shaharsery/5V-Power-Bank/Battery Charger Rev 0.4/Battery Charger Rev 0.4.sch

## KiCad design Battery Charger Rev 0.4/Battery Charger Rev 0.4.sch (2020-07-28)

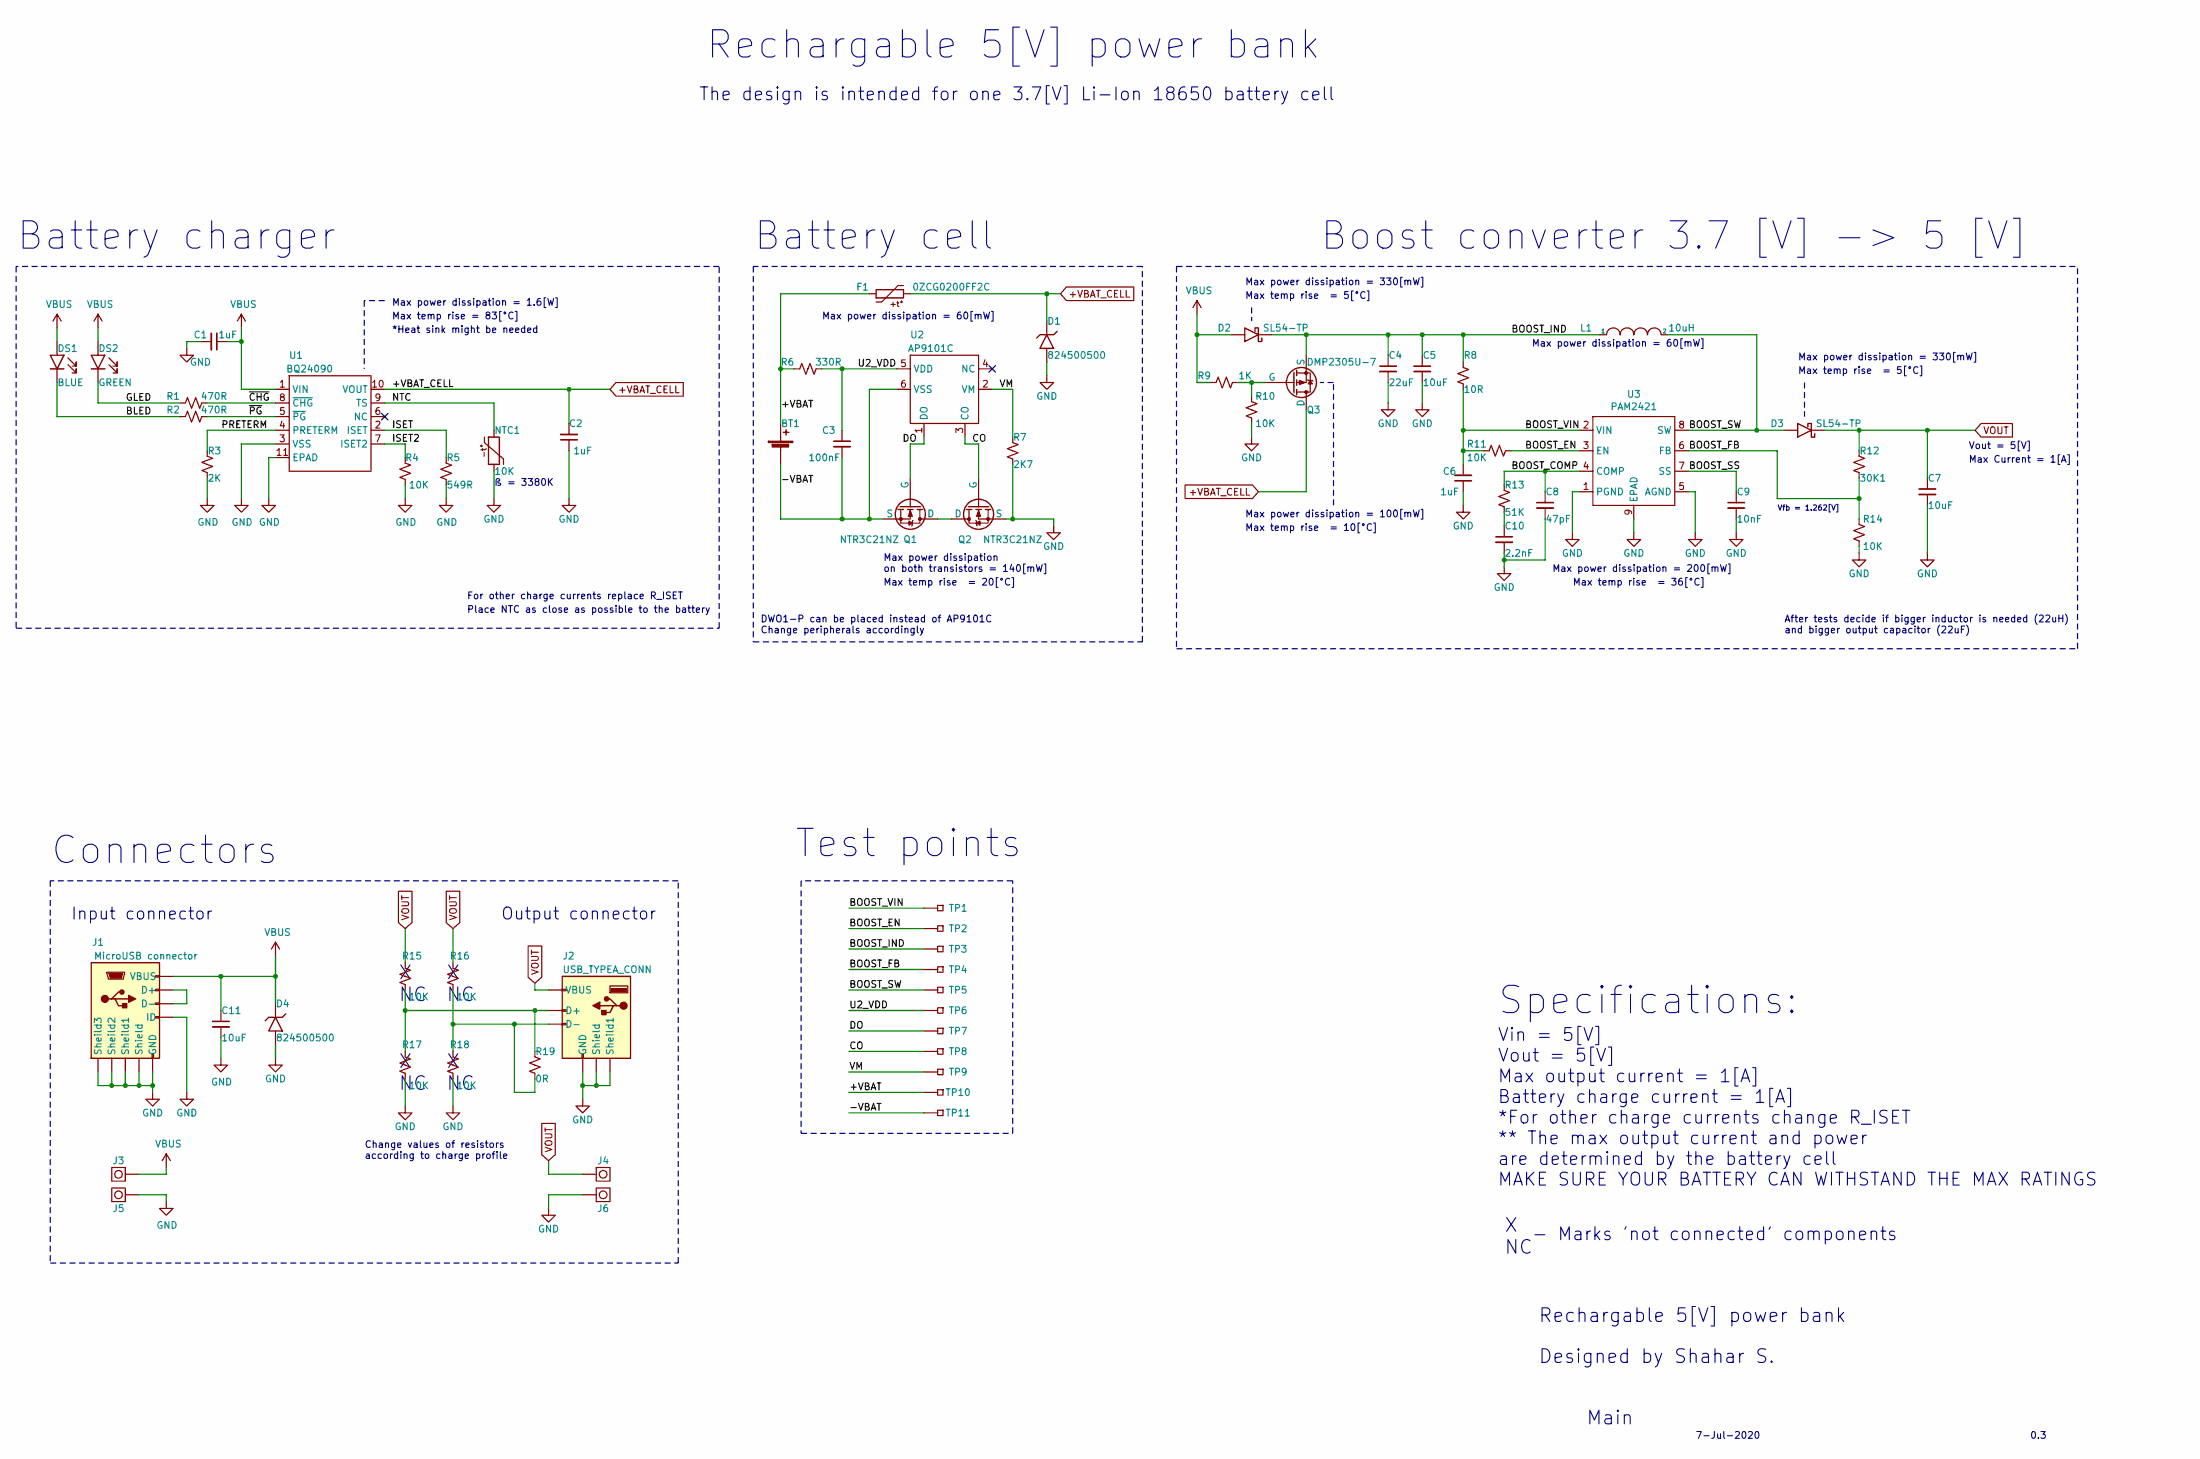
[picture p16: schematic Battery Charger Rev 0.4.sch]

Parts:
BT1: 18650 Li-ion Battery Cell
C1, C2, C6: CAPC_1uF_0603; C_0603_1608Metric_Pad1.05x0.95mm_HandSolder; Manufacturer_PN CL10B105MO8NNWC
C3: CAPC_100nF_0603; C_0603_1608Metric_Pad1.05x0.95mm_HandSolder; Manufacturer_PN CC0603KRX7R8BB104
C4: CAPC_22uF_1210; C_1210_3225Metric_Pad1.42x2.65mm_HandSolder; Manufacturer_PN C1210C226K4PACTU
C5: CAPC_10uF_0805; C_0805_2012Metric_Pad1.15x1.40mm_HandSolder; Manufacturer_PN C0805C106K4PACTU
C7: CAPC_10uF_1210; C_1210_3225Metric_Pad1.42x2.65mm_HandSolder; Manufacturer_PN C1210C106M4PACTU
C8: CAPC_47pF_0603; C_0603_1608Metric_Pad1.05x0.95mm_HandSolder; Manufacturer_PN C0603C470J1GACTU
C9: CAPC_10nF_0603; C_0603_1608Metric_Pad1.05x0.95mm_HandSolder; Manufacturer_PN CC0603KRX7R9BB103
C10: CAPC_2.2nF_0603; C_0603_1608Metric_Pad1.05x0.95mm_HandSolder; Manufacturer_PN C0603C222J5RACTU
C11: CAPC_10uF_0603; C_0603_1608Metric_Pad1.05x0.95mm_HandSolder; Manufacturer_PN GRM188R61E106KA73D
D1, D4: TVS_5V_9.2V_DO214AC; Manufacturer_PN 824500500
D2, D3: Schottky_40V_5A_DO-214AB; Manufacturer_PN SL54-TP
DS1: LEDC_BLUE_0603; LED_0603_1608Metric_Pad1.05x0.95mm_HandSolder; Manufacturer_PN 150060BS75000
DS2: LEDC_GREEN_0603; LED_0603_1608Metric_Pad1.05x0.95mm_HandSolder; Manufacturer_PN 150060VS75000
F1: PTC_POLYFUSE_8V_2A_1812; Manufacturer_PN 0ZCG0200FF2C
J1: Micro_USB_CONN; Manufacturer_PN MCR-B-S-RA-SMT-EH4B-T/R
J2: USB-A_CONN; Manufacturer_PN 292303-1
J3, J4, J5, J6: 1POS_CONN_PAD_30X30MM_H1MM; Manufacturer_PN N/A
L1: INDC_10uH_CDRH104R; Manufacturer_PN CDRH104RNP-100NC
NTC1: NTC_10K_3380K_0603; Manufacturer_PN NCU18XH103F60RB
Q1, Q2: NMOS_20V_3.6A_SOT-23-3; Manufacturer_PN NTR3C21NZT1G
Q3: PMOS_20V_4.2A_SOT-23-3; Manufacturer_PN DMP2305U-7
R1, R2: RESC_470R_0603; R_0603_1608Metric_Pad1.05x0.95mm_HandSolder; Manufacturer_PN RC0603JR-07470RL
R3: RESC_2K_0603; R_0603_1608Metric_Pad1.05x0.95mm_HandSolder; Manufacturer_PN RK73H1JTTD2001F
R4, R10, R11, R14, R15, R16, R17, R18: RESC_10K_0603; R_0603_1608Metric_Pad1.05x0.95mm_HandSolder; Manufacturer_PN RNCP0603FTD10K0
R5: RESC_549R_0603; R_0603_1608Metric_Pad1.05x0.95mm_HandSolder; Manufacturer_PN RK73H1JTTD5490F
R6: RESC_330R_0603; R_0603_1608Metric_Pad1.05x0.95mm_HandSolder; Manufacturer_PN ERJ-3EKF3300V
R7: RESC_2K7_0603; R_0603_1608Metric_Pad1.05x0.95mm_HandSolder; Manufacturer_PN CRGCQ0603F2K7
R8: RESC_10R_0603; R_0603_1608Metric_Pad1.05x0.95mm_HandSolder; Manufacturer_PN CRGH0603J10R
R9: RESC_1K_0603; R_0603_1608Metric_Pad1.05x0.95mm_HandSolder; Manufacturer_PN RC0603JR-071KL
R12: RESC_30K1_0603; R_0603_1608Metric_Pad1.05x0.95mm_HandSolder; Manufacturer_PN RMCF0603FT30K1
R13: RESC_51K_0603; R_0603_1608Metric_Pad1.05x0.95mm_HandSolder; Manufacturer_PN RMCF0603FT51K0
R19: RESC_0R_0603; R_0603_1608Metric_Pad1.05x0.95mm_HandSolder; Manufacturer_PN RC0603JR-070RL
TP1, TP2, TP3, TP4, TP5, TP6, TP7, TP8, TP9, TP10, TP11: TP_12.5X12.5_MM; Manufacturer_PN N/A
U1: BQ24090DGQR; Manufacturer_PN BQ24090DGQR
U2: AP9101C; SOT-23-6_Handsoldering; Manufacturer_PN AP9101CK6-ADTRG1
U3: PAM2421; Manufacturer_PN PAM2421AECADJR

Connections:
+VBAT: BT1.1 (+), F1.1, R6.2, TP10.1
+VBAT_CELL: C2.2, D1.K, F1.2, Q3.D, U1.10 (VOUT)
-VBAT: BT1.2 (-), C3.2, Q1.S, TP11.1, U2.6 (VSS)
BLED: DS1.K, R2.2
BOOST_COMP: C8.1, R13.1, U3.4 (COMP)
BOOST_EN: R11.2, TP2.1, U3.3 (EN)
BOOST_FB: R12.2, R14.2, TP4.1, U3.6 (FB)
BOOST_IND: C4.1, C5.1, D2.K, L1.1, Q3.S, R8.1, TP3.1
BOOST_SS: C9.1, U3.7 (SS)
BOOST_SW: D3.A, L1.2, TP5.1, U3.8 (SW)
BOOST_VIN: C6.2, R8.2, R11.1, TP1.1, U3.2 (VIN)
CO: Q2.G, TP8.1, U2.3 (CO)
DO: Q1.G, TP7.1, U2.1 (DO)
GLED: DS2.K, R1.2
GND: C1.2, C2.1, C4.2, C5.2, C6.1, C7.2, C8.2, C9.2, C10.2, C11.2, D1.A, D4.A, J1.4 (ID), J1.5 (GND), J1.6 (Shield), J1.7 (Sheild1), J1.8 (Sheild2), J1.9 (Sheild3), J2.4 (GND), J2.5 (Shield), J2.~ (Sheild1), J5.1, J6.1, NTC1.2, Q2.S, R3.2, R4.1, R5.2, R7.2, R10.1, R14.1, R17.1, R18.1, U1.3 (VSS), U1.11 (EPAD), U3.1 (PGND), U3.5 (AGND), U3.9 (EPAD)
ISET: R5.1, U1.2 (ISET)
ISET2: R4.2, U1.7 (ISET2)
NTC: NTC1.1, U1.9 (TS)
unnamed: C10.1, R13.2
unnamed: J1.2 (D-), J1.3 (D+)
unnamed: J2.2 (D-), R16.1, R18.2, R19.2
unnamed: J2.3 (D+), R15.1, R17.2, R19.1
unnamed: Q1.D, Q2.D
unnamed: Q3.G, R9.1, R10.2
PRETERM: R3.1, U1.4 (PRETERM)
U2_VDD: C3.1, R6.1, TP6.1, U2.5 (VDD)
VBUS: C1.1, C11.1, D2.A, D4.K, DS1.A, DS2.A, J1.1 (VBUS), J3.1, R9.2, U1.1 (VIN)
VM: R7.1, TP9.1, U2.2 (VM)
VOUT: C7.1, D3.K, J2.1 (VBUS), J4.1, R12.1, R15.2, R16.2
~CHG: R1.1, U1.8 (~CHG)
~PG: R2.1, U1.5 (~PG)

Notes on the sheet:
Vout = 5[V]
Change values of resistors according to charge profile
Max Current = 1[A]
Vfb = 1.262[V]
DWO1-P can be placed instead of AP9101C Change peripherals accordingly
Max power dissipation = 60[mW]
Battery cell
Boost converter 3.7 [V] -> 5 [V]
Connectors
Rechargable 5[V] power bank
Test points
Specifications:
Vin = 5[V] Vout = 5[V] Max output current = 1[A] Battery charge current = 1[A] *For other charge currents change R_ISET ** The max output current and power are determined by the battery cell MAKE SURE YOUR BATTERY CAN WITHSTAND THE MAX RATINGS
The design is intended for one 3.7[V] Li-Ion 18650 battery cell
X NC
After tests decide if bigger inductor is needed (22uH) and bigger output capacitor (22uF)
Designed by Shahar S.
7-Jul-2020
0.3
Main
- Marks 'not connected' components
Max power dissipation = 200[mW]
Max temp rise = 36[°C]
Max power dissipation on both transistors = 140[mW]
Input connector
Output connector
Max power dissipation = 100[mW]
Max temp rise = 20[°C]
Max power dissipation = 330[mW]
Max temp rise = 5[°C]
Max temp rise = 10[°C]
*Heat sink might be needed
For other charge currents replace R_ISET
Max temp rise = 83[°C]
Max power dissipation = 1.6[W]
Battery charger
Place NTC as close as possible to the battery
ß = 3380K
